MechRedPanda/red-panda-afm/cad/afm/StepMotorUpperFrame.step

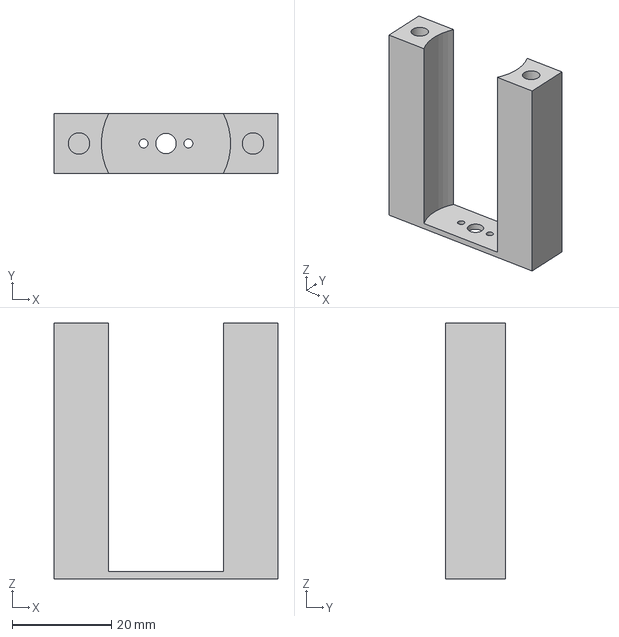
[picture p17: CAD file, 2025-06-06]
cad/afm/StepMotorUpperFrame.step
45.0 x 12.0 x 51.5 mm
