MechRedPanda/red-panda-afm/cad/afm/StepMotorUpperFrame2.step

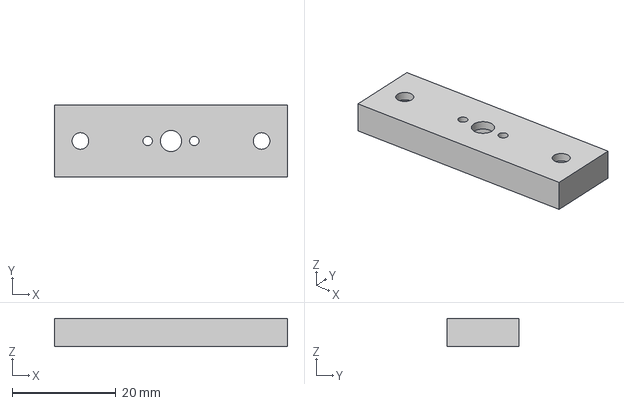
[picture p18: CAD file, 2025-06-06]
cad/afm/StepMotorUpperFrame2.step
45.0 x 14.0 x 5.50 mm
