MechRedPanda/red-panda-afm/cad/afm/KnobAdaptor.step

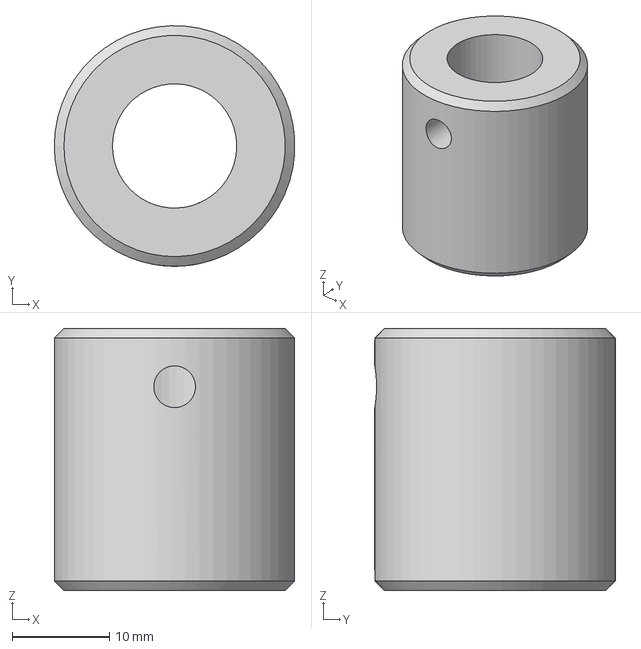
[picture p19: CAD file, 2025-06-06]
cad/afm/KnobAdaptor.step
24.8 x 24.8 x 27.0 mm
