MechRedPanda/red-panda-afm/cad/afm/ProbeHolderAdaptor.step

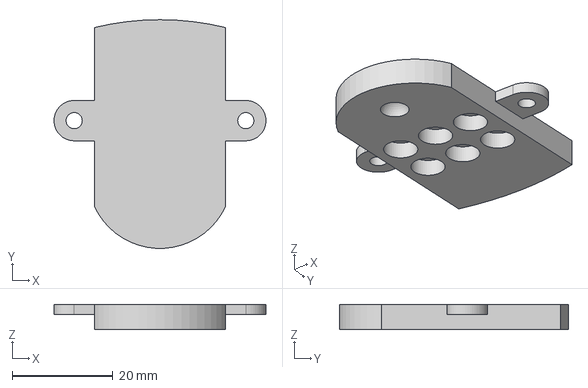
[picture p20: CAD file, 2025-06-06]
cad/afm/ProbeHolderAdaptor.step
42.0 x 45.3 x 5.00 mm
