MechRedPanda/red-panda-afm/cad/afm/StepMotorUpperFrame1.step

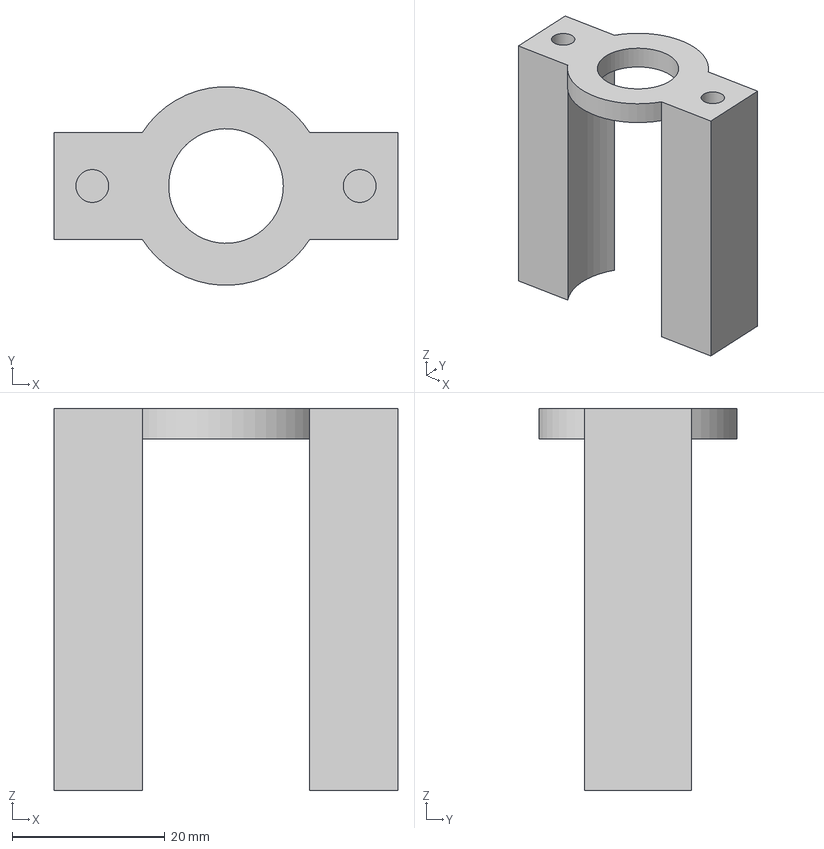
[picture p21: CAD file, 2025-06-06]
cad/afm/StepMotorUpperFrame1.step
45.0 x 26.0 x 50.0 mm
