MechRedPanda/red-panda-afm/cad/afm/PiezoAdaptor.step

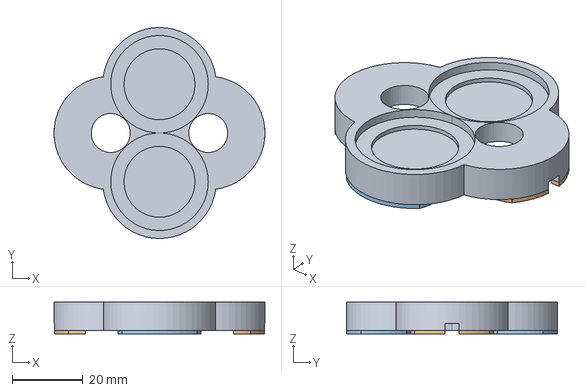
[picture p22: CAD file, 2025-06-06]
cad/afm/PiezoAdaptor.step
59.5 x 59.5 x 9.00 mm
