MechRedPanda/red-panda-afm/cad/afm/LowerFrame.step

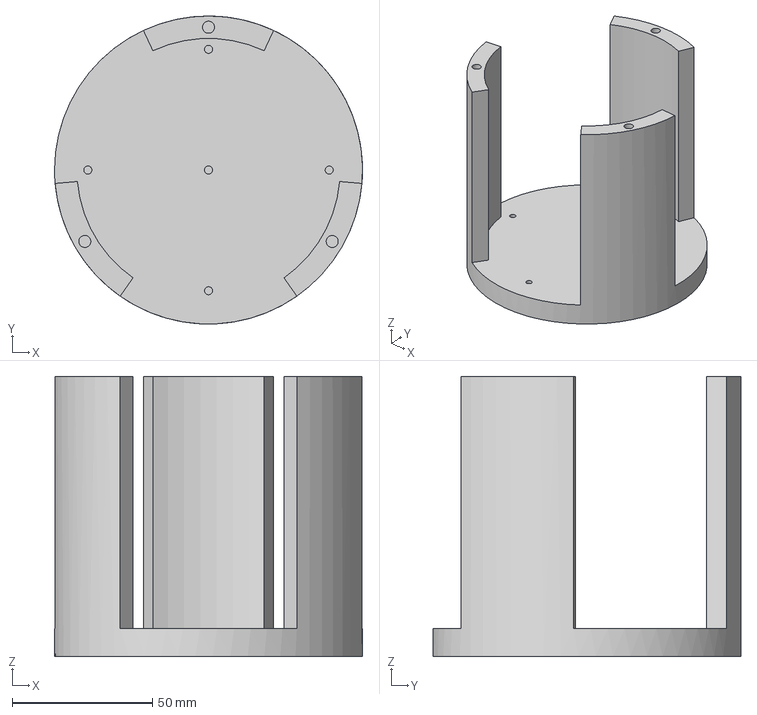
[picture p23: CAD file, 2025-06-06]
cad/afm/LowerFrame.step
110.0 x 110.0 x 100.0 mm
