MechRedPanda/red-panda-afm/cad/afm/AFM_Adaptor.step

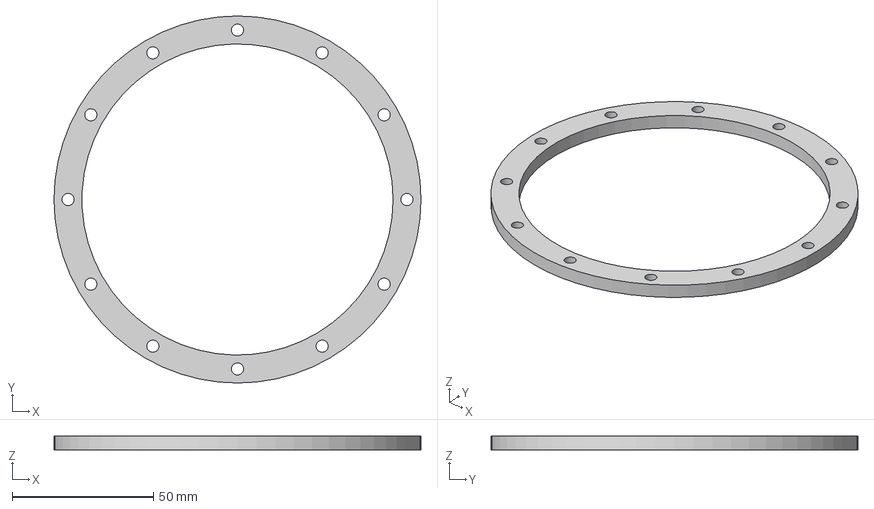
[picture p24: CAD file, 2025-06-06]
cad/afm/AFM_Adaptor.step
130.0 x 130.0 x 5.00 mm
