MechRedPanda/red-panda-afm/cad/afm/OPU_Tuning_Stand.step

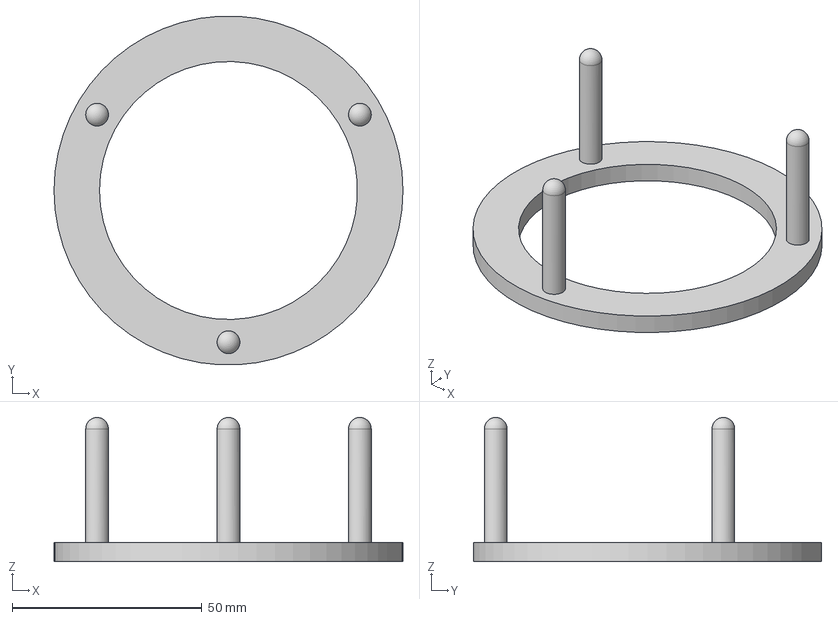
[picture p25: CAD file, 2025-06-06]
cad/afm/OPU_Tuning_Stand.step
92.0 x 91.9 x 38.0 mm
