MechRedPanda/red-panda-afm/cad/afm/SpringExtension.step

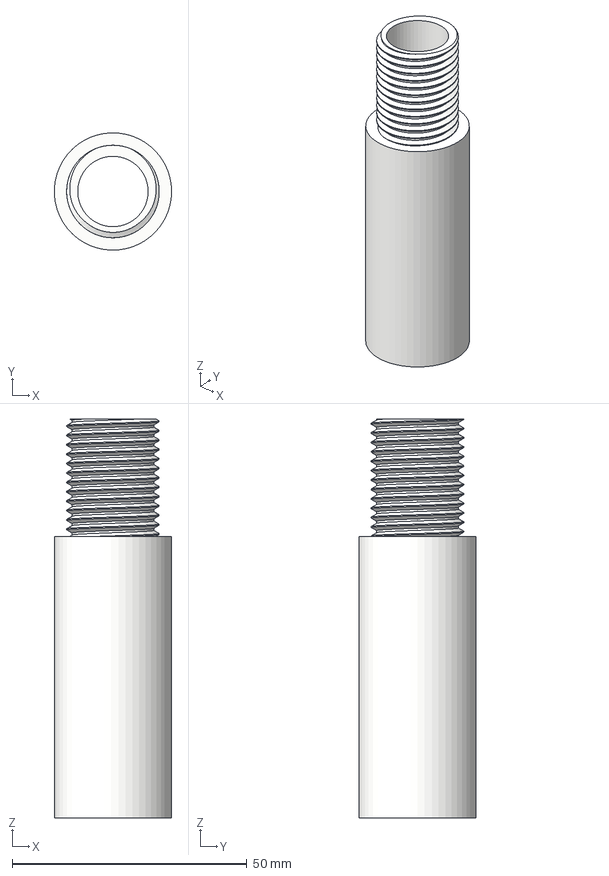
[picture p26: CAD file, 2025-06-06]
cad/afm/SpringExtension.step
25.0 x 25.0 x 85.0 mm
